sadekbaroudi/bykeeb/cases/carrying-case/hinge-assembly-required/bykeeb-carrying-case-20.7mm-inner-depth-left.stl

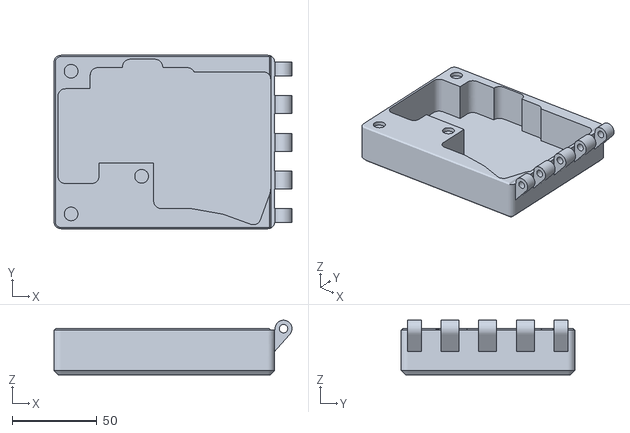
[picture p24: CAD file, 2024-08-18]
cases/carrying-case/hinge-assembly-required/bykeeb-carrying-case-20.7mm-inner-depth-left.stl
140.2 x 102.2 x 32.2
