sadekbaroudi/bykeeb/cases/bykeeb-body-right-inset-0.2mm.stl

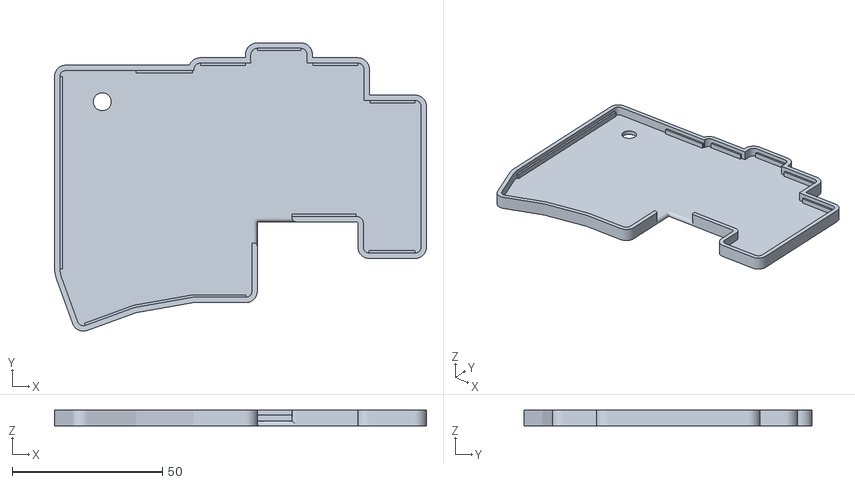
[picture p25: CAD file, 2024-08-09]
cases/bykeeb-body-right-inset-0.2mm.stl
124.0 x 96.1 x 5.20
