sadekbaroudi/bykeeb/cases/carrying-case/hinge-assembly-required/bykeeb-carrying-case-hinge-center-piece.stl

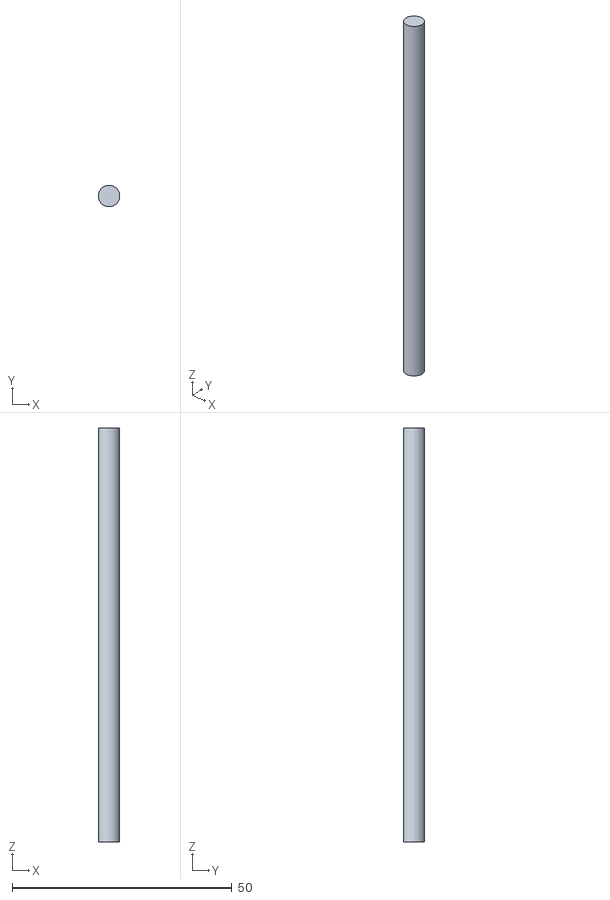
[picture p26: CAD file, 2024-08-16]
cases/carrying-case/hinge-assembly-required/bykeeb-carrying-case-hinge-center-piece.stl
4.89 x 4.89 x 94.3
