sadekbaroudi/bykeeb/cases/bykeeb-on-off-switch-long-left.stl

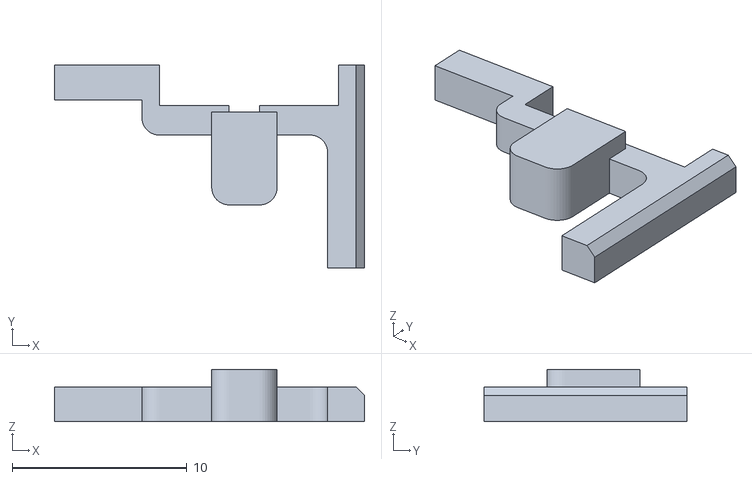
[picture p27: CAD file, 2024-07-13]
cases/bykeeb-on-off-switch-long-left.stl
17.8 x 11.6 x 3.00
