sadekbaroudi/bykeeb/cases/bykeeb-on-off-switch-short-right.stl

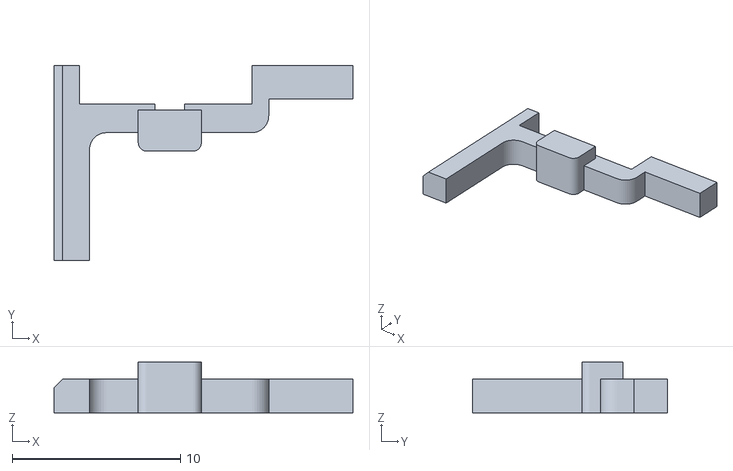
[picture p28: CAD file, 2024-07-13]
cases/bykeeb-on-off-switch-short-right.stl
17.8 x 11.6 x 3.00
