sadekbaroudi/bykeeb/cases/bykeeb-switchplate-choc-or-glp-alphas.stl

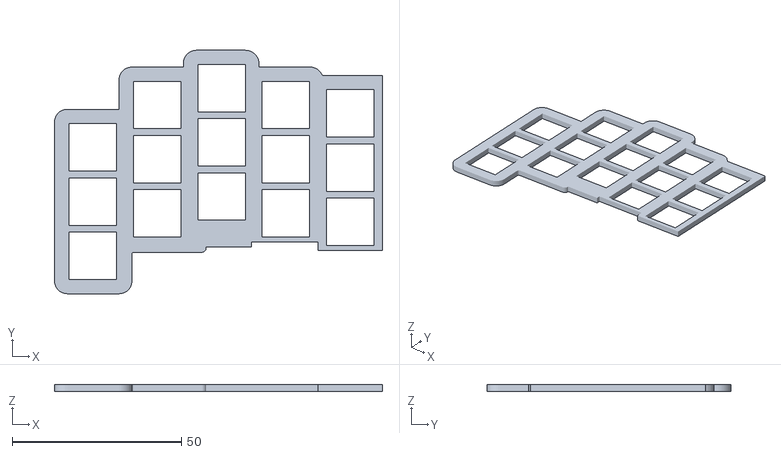
[picture p29: CAD file, 2024-07-11]
cases/bykeeb-switchplate-choc-or-glp-alphas.stl
96.8 x 71.9 x 2.10
