sadekbaroudi/bykeeb/cases/bykeeb-switchplate-choc-or-glp-thumbs.stl

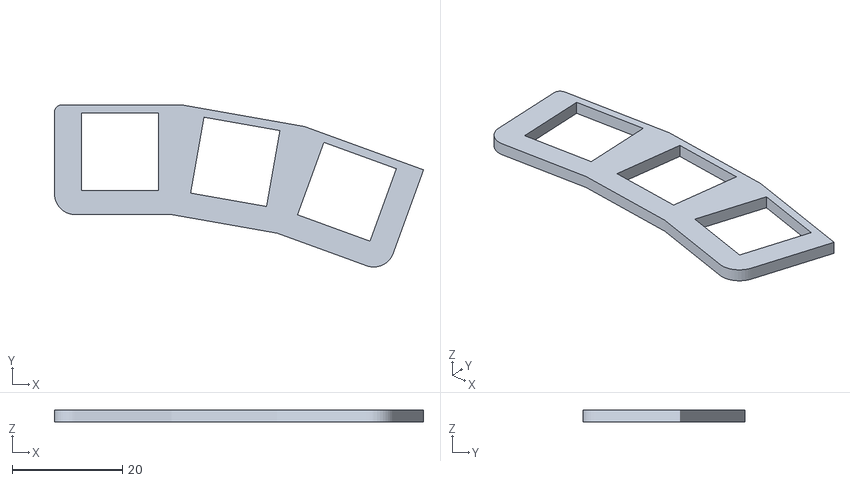
[picture p30: CAD file, 2024-07-11]
cases/bykeeb-switchplate-choc-or-glp-thumbs.stl
67.0 x 29.4 x 2.10
