sadekbaroudi/bykeeb/cases/bykeeb-switchplate-mx-alphas.stl

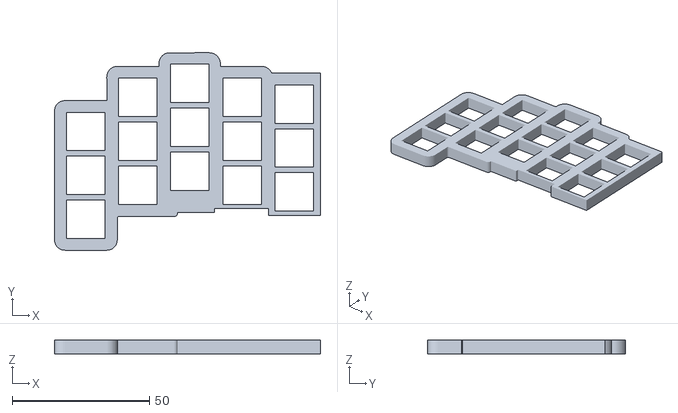
[picture p31: CAD file, 2024-07-11]
cases/bykeeb-switchplate-mx-alphas.stl
96.8 x 71.9 x 5.00
