sadekbaroudi/bykeeb/cases/bykeeb-switchplate-mx-thumbs.stl

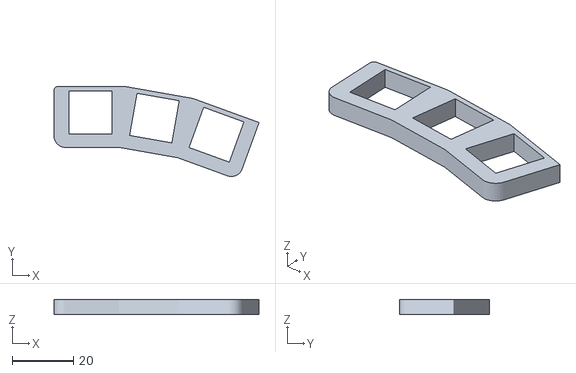
[picture p32: CAD file, 2024-07-11]
cases/bykeeb-switchplate-mx-thumbs.stl
67.0 x 29.4 x 5.00
